willwaush/Cenere-Mouse/Kicad Files/Extra Libs/pmw3360dm-mouse-sensor-1.snapshot.1/renderv2.PNG

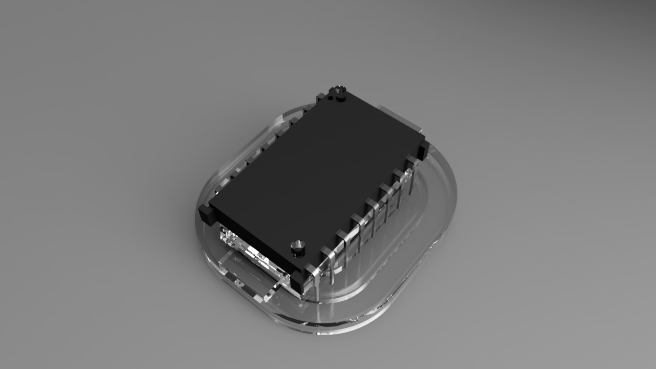
Kicad Files/Extra Libs/pmw3360dm-mouse-sensor-1.snapshot.1/renderv2.PNG
